WilliamLayne/lambda-sstc/Case/production-files/meshes/PCB_Standoff.3MF

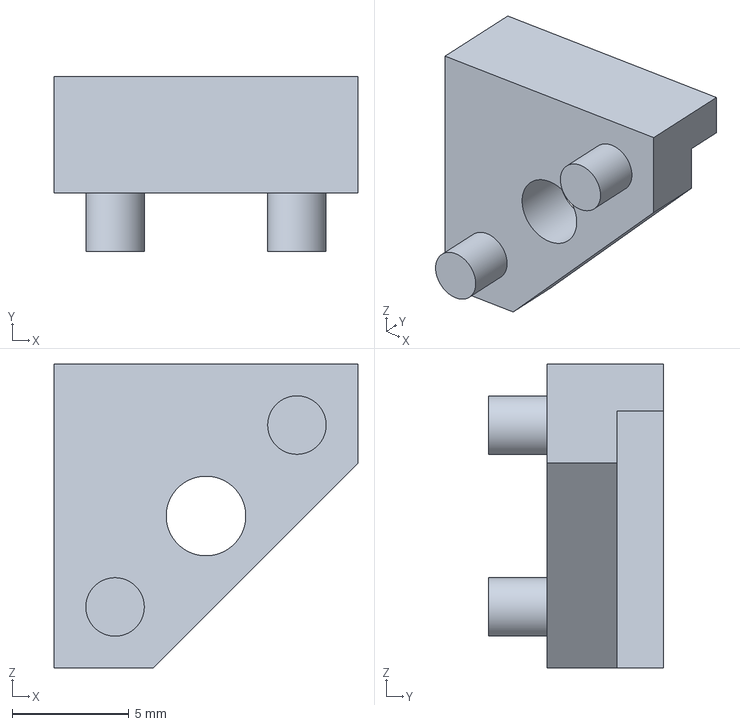
[picture p13: CAD file, 2026-08-24]
Case/production-files/meshes/PCB_Standoff.3MF
13.0 x 7.50 x 13.0 mm
