WilliamLayne/lambda-sstc/Case/Panel_Left.SLDPRT

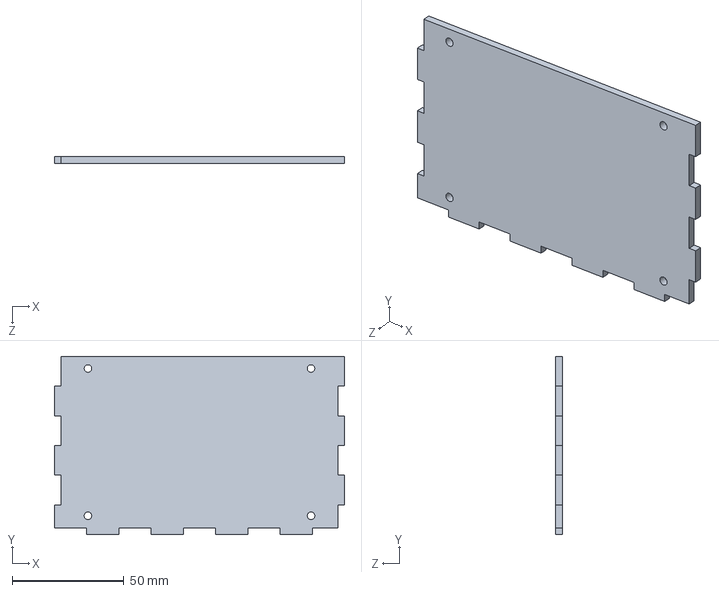
[picture p14: CAD file, 2026-08-10]
Case/Panel_Left.SLDPRT
130.0 x 80.0 x 3.00 mm
