WilliamLayne/lambda-sstc/Case/production-files/drawings/Panel_Back.DXF

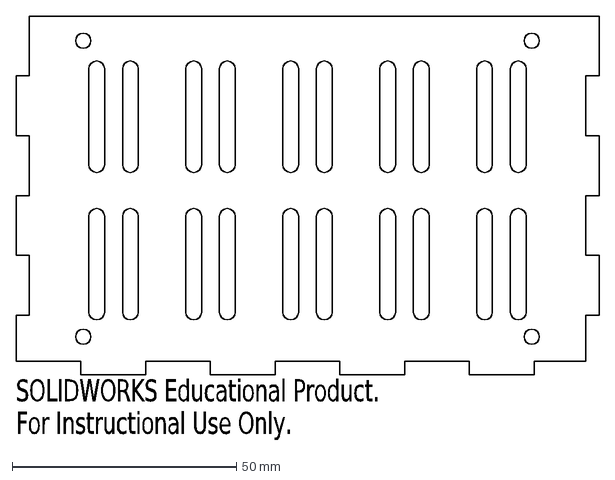
[picture p15: CAD file, 2026-08-10]
Case/production-files/drawings/Panel_Back.DXF
SOLIDWORKS Educational Product.
For Instructional Use Only.
