WilliamLayne/lambda-sstc/Case/production-files/meshes/Primary_Form.3MF

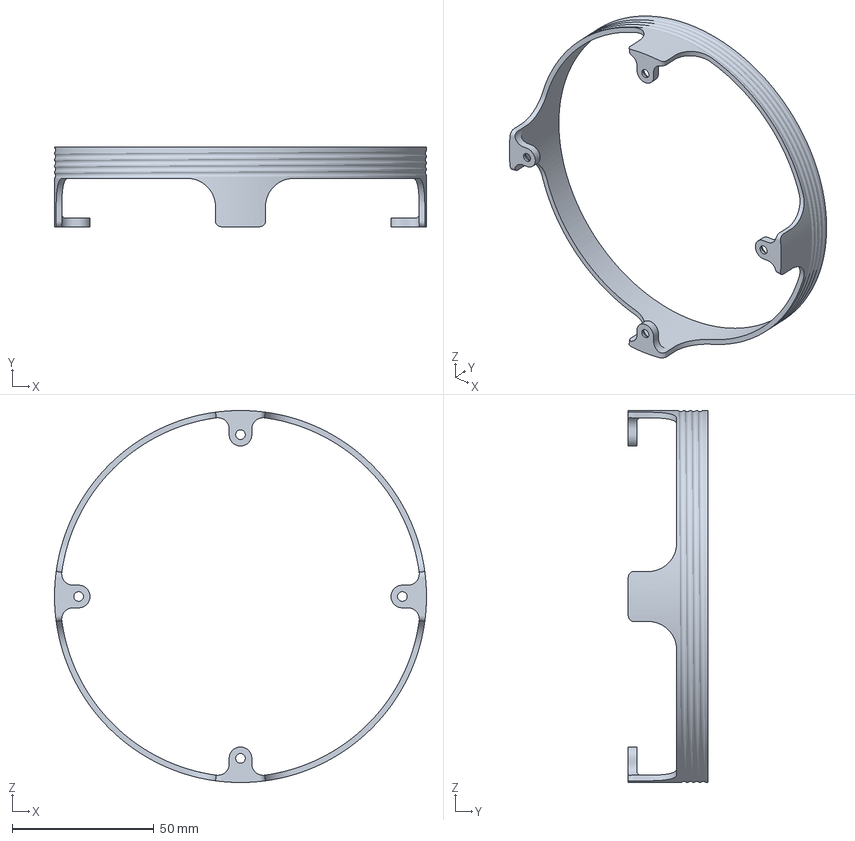
[picture p16: CAD file, 2026-08-24]
Case/production-files/meshes/Primary_Form.3MF
131.0 x 28.0 x 131.0 mm
