WilliamLayne/lambda-sstc/Case/production-files/drawings/Panel_Top.DXF

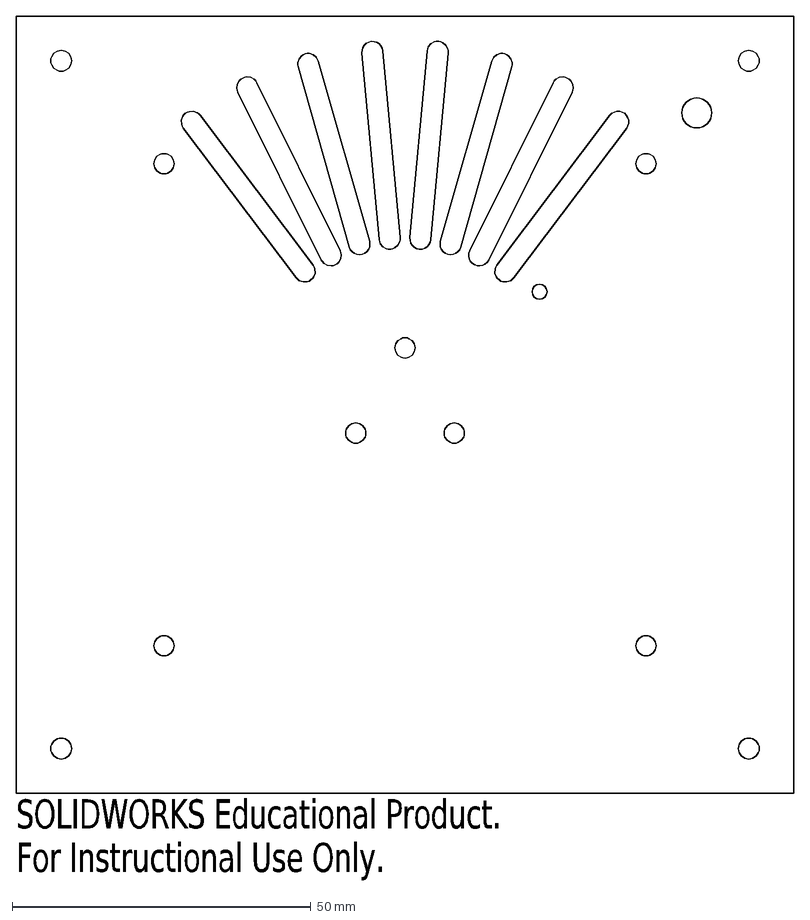
[picture p17: CAD file, 2026-08-10]
Case/production-files/drawings/Panel_Top.DXF
SOLIDWORKS Educational Product.
For Instructional Use Only.
