WilliamLayne/lambda-sstc/Case/Heatsink.SLDPRT

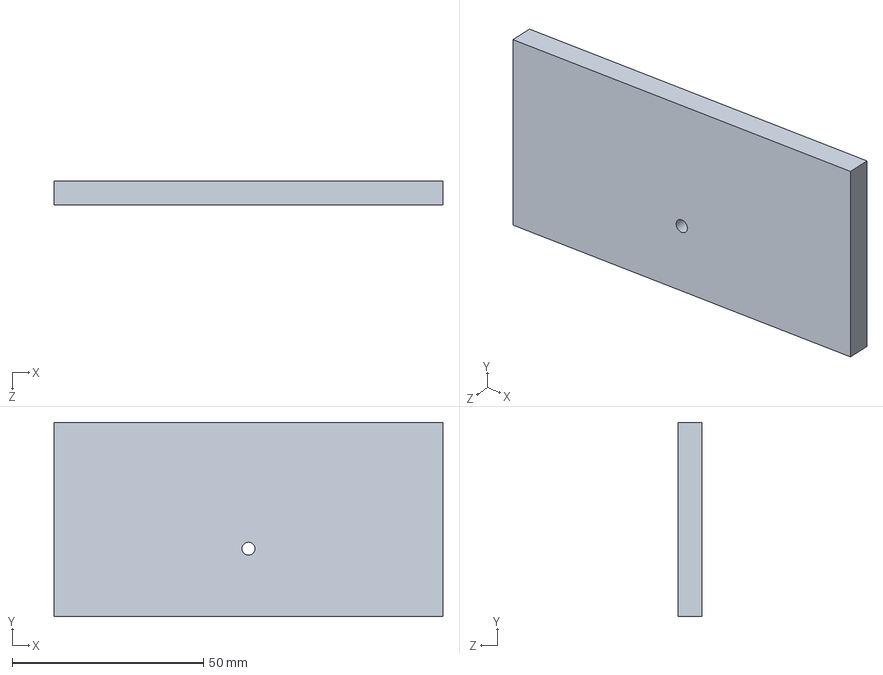
[picture p18: CAD file, 2026-05-22]
Case/Heatsink.SLDPRT
101.6 x 50.8 x 6.35 mm
