WilliamLayne/lambda-sstc/Case/Switch_Test.SLDPRT

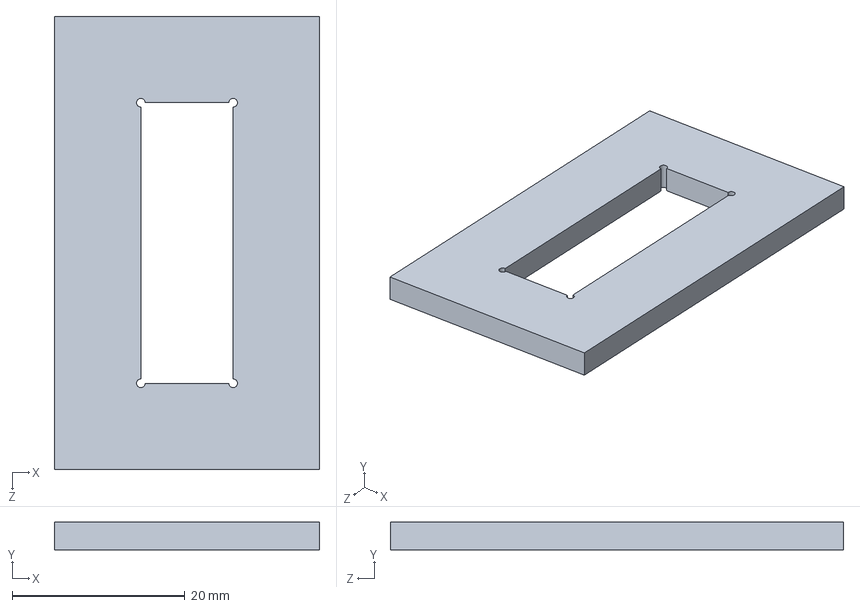
[picture p19: CAD file, 2026-05-16]
Case/Switch_Test.SLDPRT
30.7 x 3.20 x 52.5 mm
