WilliamLayne/lambda-sstc/Case/M3n.SLDPRT

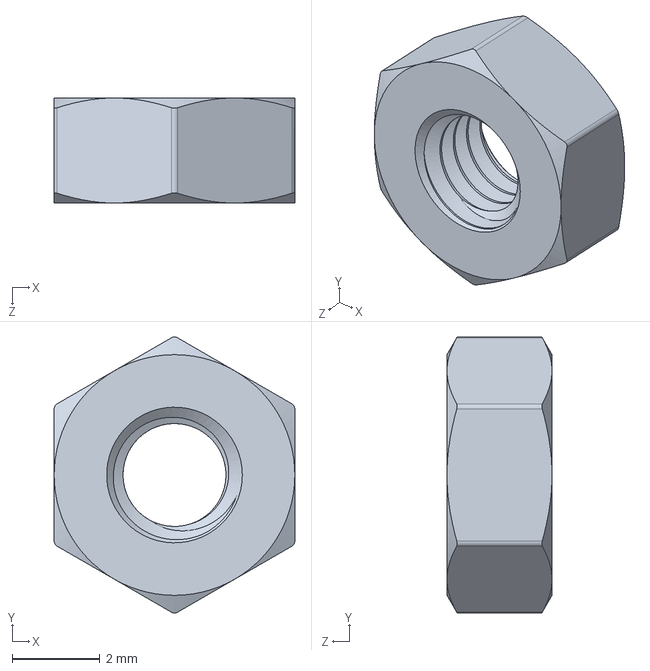
[picture p20: CAD file, 2026-05-16]
Case/M3n.SLDPRT
5.50 x 6.31 x 2.40 mm
