WilliamLayne/lambda-sstc/Case/Breakout_Point.SLDPRT

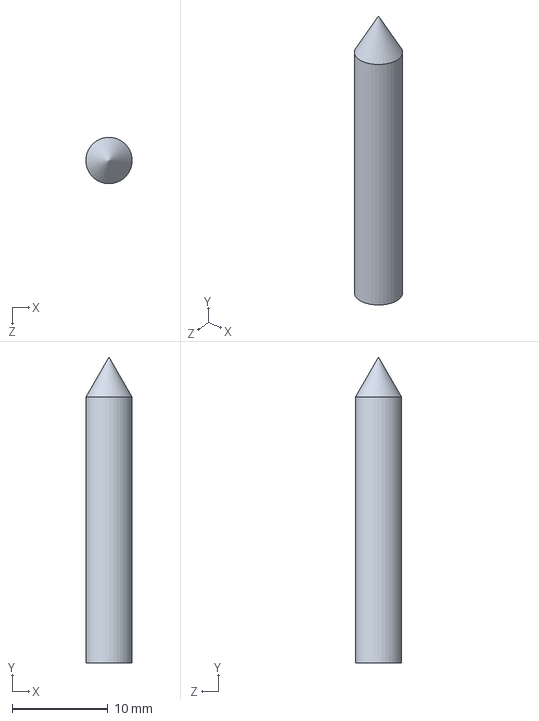
[picture p21: CAD file, 2026-05-16]
Case/Breakout_Point.SLDPRT
4.85 x 32.0 x 4.85 mm
