WilliamLayne/lambda-sstc/Case/Secondary_Form.SLDPRT

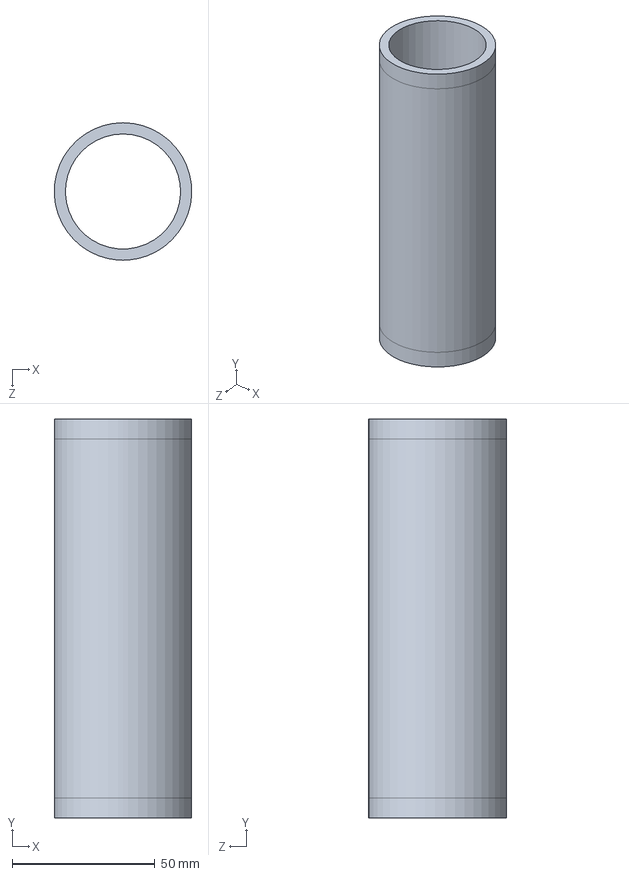
[picture p22: CAD file, 2026-05-16]
Case/Secondary_Form.SLDPRT
48.2 x 140.0 x 48.3 mm
